1847123212/High-Speed-FPGA-based-Data-Acquisition-System-100MSPS/vhdl files/aux_vlad.vhd

library IEEE;
use IEEE.STD_LOGIC_1164.all;

use ieee.std_logic_unsigned.all;
use ieee.std_logic_arith.all;   
package aux is

function ascii_2_std_logic_vector(ch: character) return std_logic_vector;
function std_logic_vector_2_ascii(vec: std_logic_vector(7 downto 0)) return character;
function reverse_vector (a: in std_logic_vector) return std_logic_vector ;
end aux;

package body aux is
function ascii_2_std_logic_vector(ch: character) return std_logic_vector is
variable out_vector: std_logic_vector(7 downto 0);                         
begin                                                                      
  case ch is                                                               
    when 'a' => out_vector := conv_std_logic_vector(97,8);                 
    when 'b' => out_vector := conv_std_logic_vector(98,8);                 
    when 'c' => out_vector := conv_std_logic_vector(99,8);                 
    when 'd' => out_vector := conv_std_logic_vector(100,8);                
    when 'e' => out_vector := conv_std_logic_vector(101,8);                
    when 'f' => out_vector := conv_std_logic_vector(102,8);                
    when 'g' => out_vector := conv_std_logic_vector(103,8);                
    when 'h' => out_vector := conv_std_logic_vector(104,8);                
    when 'i' => out_vector := conv_std_logic_vector(105,8);                
    when 'j' => out_vector := conv_std_logic_vector(106,8);                
    when 'k' => out_vector := conv_std_logic_vector(107,8);                
    when 'l' => out_vector := conv_std_logic_vector(108,8);                
    when 'm' => out_vector := conv_std_logic_vector(109,8);                
    when 'n' => out_vector := conv_std_logic_vector(110,8);                
    when 'o' => out_vector := conv_std_logic_vector(111,8);                
    when 'p' => out_vector := conv_std_logic_vector(112,8);                
    when 'q' => out_vector := conv_std_logic_vector(113,8);                
    when 'r' => out_vector := conv_std_logic_vector(114,8);                
    when 's' => out_vector := conv_std_logic_vector(115,8);                
    when 't' => out_vector := conv_std_logic_vector(116,8);                
    when 'u' => out_vector := conv_std_logic_vector(117,8);                
    when 'v' => out_vector := conv_std_logic_vector(118,8);                
    when 'w' => out_vector := conv_std_logic_vector(119,8);                
    when 'x' => out_vector := conv_std_logic_vector(120,8);                
    when 'y' => out_vector := conv_std_logic_vector(121,8);                
    when 'z' => out_vector := conv_std_logic_vector(122,8);                
                                                                           
    when 'A' => out_vector := conv_std_logic_vector(65,8);                 
    when 'B' => out_vector := conv_std_logic_vector(66,8);                 
    when 'C' => out_vector := conv_std_logic_vector(67,8);                 
    when 'D' => out_vector := conv_std_logic_vector(68,8);                 
    when 'E' => out_vector := conv_std_logic_vector(69,8);                 
    when 'F' => out_vector := conv_std_logic_vector(70,8);                 
    when 'G' => out_vector := conv_std_logic_vector(71,8);                 
    when 'H' => out_vector := conv_std_logic_vector(72,8);                 
    when 'I' => out_vector := conv_std_logic_vector(73,8);                 
    when 'J' => out_vector := conv_std_logic_vector(74,8);                 
    when 'K' => out_vector := conv_std_logic_vector(75,8);                 
    when 'L' => out_vector := conv_std_logic_vector(76,8);                 
    when 'M' => out_vector := conv_std_logic_vector(77,8);                 
    when 'N' => out_vector := conv_std_logic_vector(78,8);                 
    when 'O' => out_vector := conv_std_logic_vector(79,8);                 
    when 'P' => out_vector := conv_std_logic_vector(80,8);                 
    when 'Q' => out_vector := conv_std_logic_vector(81,8);                 
    when 'R' => out_vector := conv_std_logic_vector(82,8);                 
    when 'S' => out_vector := conv_std_logic_vector(83,8);                 
    when 'T' => out_vector := conv_std_logic_vector(84,8);                 
    when 'U' => out_vector := conv_std_logic_vector(85,8);                 
    when 'V' => out_vector := conv_std_logic_vector(86,8);                 
    when 'W' => out_vector := conv_std_logic_vector(87,8);                 
    when 'X' => out_vector := conv_std_logic_vector(88,8);                 
    when 'Y' => out_vector := conv_std_logic_vector(89,8);                 
    when 'Z' => out_vector := conv_std_logic_vector(90,8);                 
                                                                           
    when '0' => out_vector := conv_std_logic_vector(48,8);                 
    when '1' => out_vector := conv_std_logic_vector(49,8);                 
    when '2' => out_vector := conv_std_logic_vector(50,8);                 
    when '3' => out_vector := conv_std_logic_vector(51,8);                 
    when '4' => out_vector := conv_std_logic_vector(52,8);                 
    when '5' => out_vector := conv_std_logic_vector(53,8);                 
    when '6' => out_vector := conv_std_logic_vector(54,8);                 
    when '7' => out_vector := conv_std_logic_vector(55,8);                 
    when '8' => out_vector := conv_std_logic_vector(56,8);                 
    when '9' => out_vector := conv_std_logic_vector(57,8);                 
                                                                           
    when ' ' => out_vector := conv_std_logic_vector(32,8);                 
    when '!' => out_vector := conv_std_logic_vector(33,8);                 
    --when '\"' => out_vector := conv_std_logic_vector(34,8);              
    when '#' => out_vector := conv_std_logic_vector(35,8);                 
    when '$' => out_vector := conv_std_logic_vector(36,8);                 
    when '%' => out_vector := conv_std_logic_vector(37,8);                 
    when '&' => out_vector := conv_std_logic_vector(38,8);                 
    when ''' => out_vector := conv_std_logic_vector(39,8);                 
    when '(' => out_vector := conv_std_logic_vector(40,8);                 
    when ')' => out_vector := conv_std_logic_vector(41,8);                 
    when '*' => out_vector := conv_std_logic_vector(42,8);                 
    when '+' => out_vector := conv_std_logic_vector(43,8);                 
    when ',' => out_vector := conv_std_logic_vector(44,8);                 
    when '-' => out_vector := conv_std_logic_vector(45,8);                 
    when '.' => out_vector := conv_std_logic_vector(46,8);                 
    when '/' => out_vector := conv_std_logic_vector(47,8);                 
    when ':' => out_vector := conv_std_logic_vector(58,8);                 
    when ';' => out_vector := conv_std_logic_vector(59,8);                 
    when '<' => out_vector := conv_std_logic_vector(60,8);                 
    when '=' => out_vector := conv_std_logic_vector(61,8);                 
    when '>' => out_vector := conv_std_logic_vector(62,8);                 
    when '?' => out_vector := conv_std_logic_vector(63,8);                 
    when '@' => out_vector := conv_std_logic_vector(64,8);                 
    when '[' => out_vector := conv_std_logic_vector(91,8);                 
    when '\' => out_vector := conv_std_logic_vector(92,8);                 
    when ']' => out_vector := conv_std_logic_vector(93,8);                 
    when '^' => out_vector := conv_std_logic_vector(94,8);                 
    when '_' => out_vector := conv_std_logic_vector(95,8);                 
    when '`' => out_vector := conv_std_logic_vector(96,8);                 
    when '{' => out_vector := conv_std_logic_vector(123,8);                
    when '|' => out_vector := conv_std_logic_vector(124,8);                
    when '}' => out_vector := conv_std_logic_vector(125,8);                
    when '~' => out_vector := conv_std_logic_vector(126,8);                
                                                                           
    when others => null;                                                   
  end case;                                                                
  return  out_vector;                                                      
end function  ascii_2_std_logic_vector;                                    

function std_logic_vector_2_ascii(vec: std_logic_vector(7 downto 0)) return character is
variable out_char: character;                                                           
begin                                                                                   
  case vec is                                                                           
    when "01100001" => out_char := 'a';                                                 
    when "01100010" => out_char := 'b';                                                 
    when "01100011" => out_char := 'c';                                                 
    when "01100100" => out_char := 'd';                                                 
    when "01100101" => out_char := 'e';                                                 
    when "01100110" => out_char := 'f';                                                 
    when "01100111" => out_char := 'g';                                                 
    when "01101000" => out_char := 'h';                                                 
    when "01101001" => out_char := 'i';                                                 
    when "01101010" => out_char := 'j';                                                 
    when "01101011" => out_char := 'k';                                                 
    when "01101100" => out_char := 'l';                                                 
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
    when "00110101" => out_char := '5';                                                 
    when "00110110" => out_char := '6';                                                 
    when "00110111" => out_char := '7';                                                 
    when "00111000" => out_char := '8';                                                 
    when "00111001" => out_char := '9';                                                 
                                                                                        
    when "00100000" => out_char := ' ';                                                 
    when "00100001" => out_char := '!';                                                 
    --when "00100010" => out_vector := '\"';                                            
    when "00100011" => out_char := '#';                                                 
    when "00100100" => out_char := '$';                                                 
    when "00100101" => out_char := '%';                                                 
    when "00100110" => out_char := '&';                                                 
    when "00100111" => out_char := ''';                                                 
    when "00101000" => out_char := '(';                                                 
    when "00101001" => out_char := ')';
    when "00101010" => out_char := '*';
    when "00101011" => out_char := '+';
    when "00101100" => out_char := ',';
    when "00101101" => out_char := '-';
    when "00101110" => out_char := '.';
    when "00101111" => out_char := '/';
    when "00111010" => out_char := ':';
    when "00111011" => out_char := ';';
    when "00111100" => out_char := '<';
    when "00111101" => out_char := '=';
    when "00111110" => out_char := '>';
    when "00111111" => out_char := '?';
    when "01000000" => out_char := '@';
    when "01011011" => out_char := '[';
    when "01011100" => out_char := '\';
    when "01011101" => out_char := ']';
    when "01011110" => out_char := '^';
    when "01011111" => out_char := '_';
    when "01100000" => out_char := '`';
    when "01111011" => out_char := '{';
    when "01111100" => out_char := '|';
    when "01111101" => out_char := '}';
    when "01111110" => out_char := '~';

    when others => null;
  end case;
  return  out_char;
end function  std_logic_vector_2_ascii;


function reverse_vector (a: in std_logic_vector)
return std_logic_vector is
  variable result: std_logic_vector(a'RANGE);
  alias aa: std_logic_vector(a'REVERSE_RANGE) is a;
begin
  for i in aa'RANGE loop
    result(i) := aa(i);
  end loop;
  return result;
end;


end aux;
